Scrath1/Pico-LiDAR/circuit-diagram/circuit-diagram.kicad_pcb

## KiCad design schematics/core_driver.kicad_sch

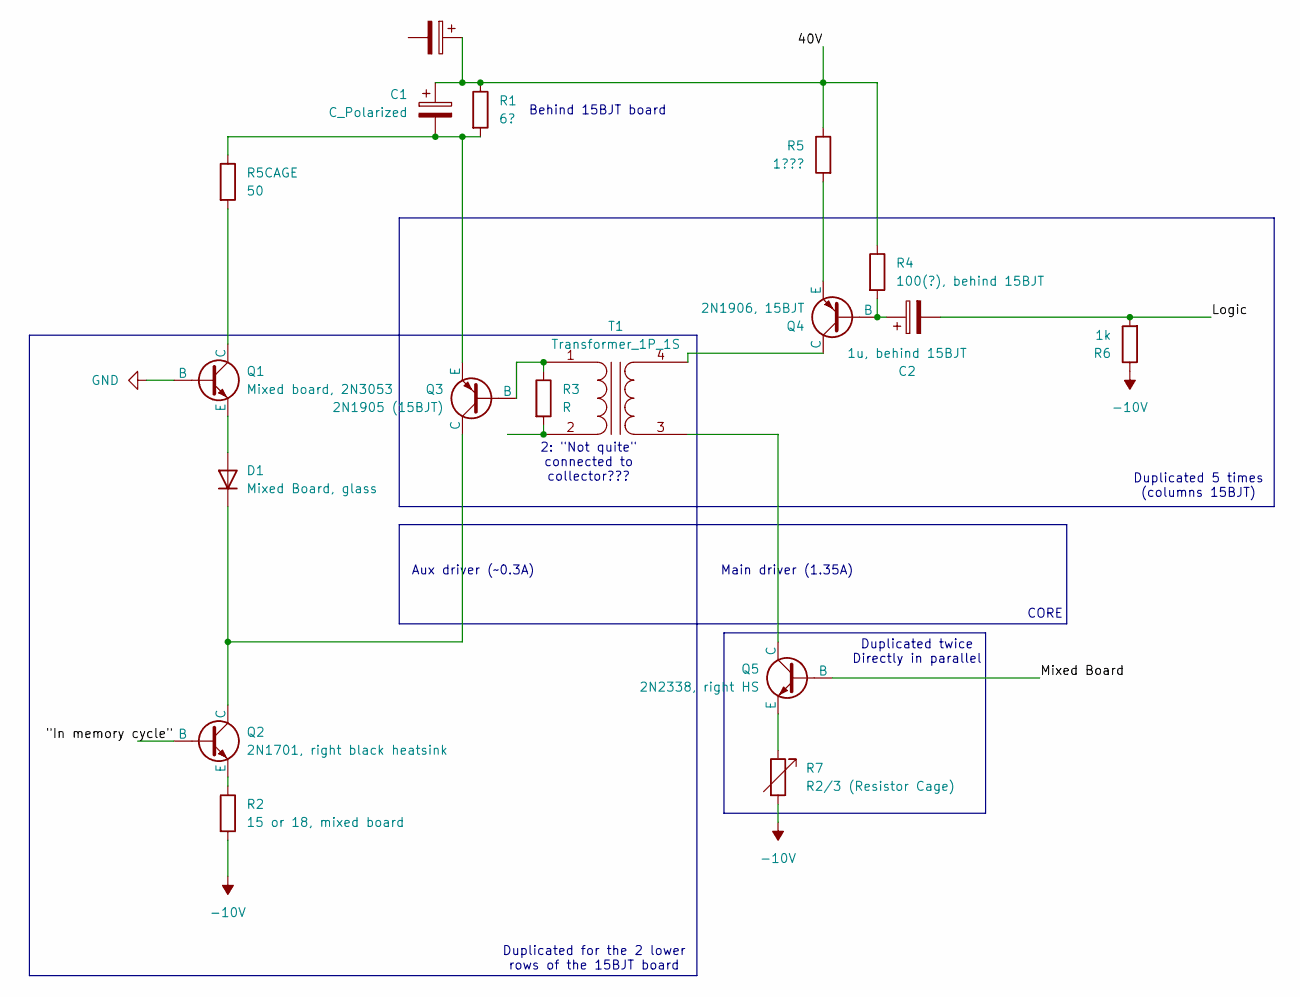
[picture p8: schematic core_driver.kicad_sch]

Parts:
C1: C_Polarized
C2: 1u, behind 15BJT
C8: 4m
D1: Mixed Board, glass
Q1: Mixed board, 2N3053
Q2: 2N1701, right black heatsink
Q3: 2N1905 (15BJT)
Q4: 2N1906, 15BJT
Q5: 2N2338, right HS
R1: 6?
R2: 15 or 18, mixed board
R3: R
R4: 100(?), behind 15BJT
R5: 1???
R5CAGE: 50
R6: 1k
R7: R2/3 (Resistor Cage)
T1: Transformer_1P_1S

Connections:
40V: C1.1, C8.1, R1.1, R4.1, R5.1
"In memory cycle": Q2.2 (B)
-10V: R2.2, R6.1, R7.2
GND: Q1.2 (B)
Logic: C2.2, R6.2
Mixed Board: Q5.2 (B)
unnamed: C1.2, Q3.3 (E), R1.2, R5CAGE.1
unnamed: C2.1, Q4.2 (B), R4.2
unnamed: D1.1 (K), Q2.1 (C), Q3.1 (C)
unnamed: D1.2 (A), Q1.3 (E)
unnamed: Q1.1 (C), R5CAGE.2
unnamed: Q2.3 (E), R2.1
unnamed: Q3.2 (B), R3.1, T1.1 (AA)
unnamed: Q4.1 (C), T1.4 (SB)
unnamed: Q4.3 (E), R5.2
unnamed: Q5.1 (C), T1.3 (SA)
unnamed: Q5.3 (E), R7.1
unnamed: R3.2, T1.2 (AB)

Notes on the sheet:
2: "Not quite" connected to collector???
Duplicated for the 2 lower rows of the 15BJT board
Duplicated 5 times (columns 15BJT)
Aux driver (~0.3A)
Main driver (1.35A)
Duplicated twice Directly in parallel
CORE
Behind 15BJT board
