Scrath1/Pico-LiDAR/circuit-diagram/circuit-diagram.kicad_pcb

## KiCad design schematics/untitled.kicad_sch

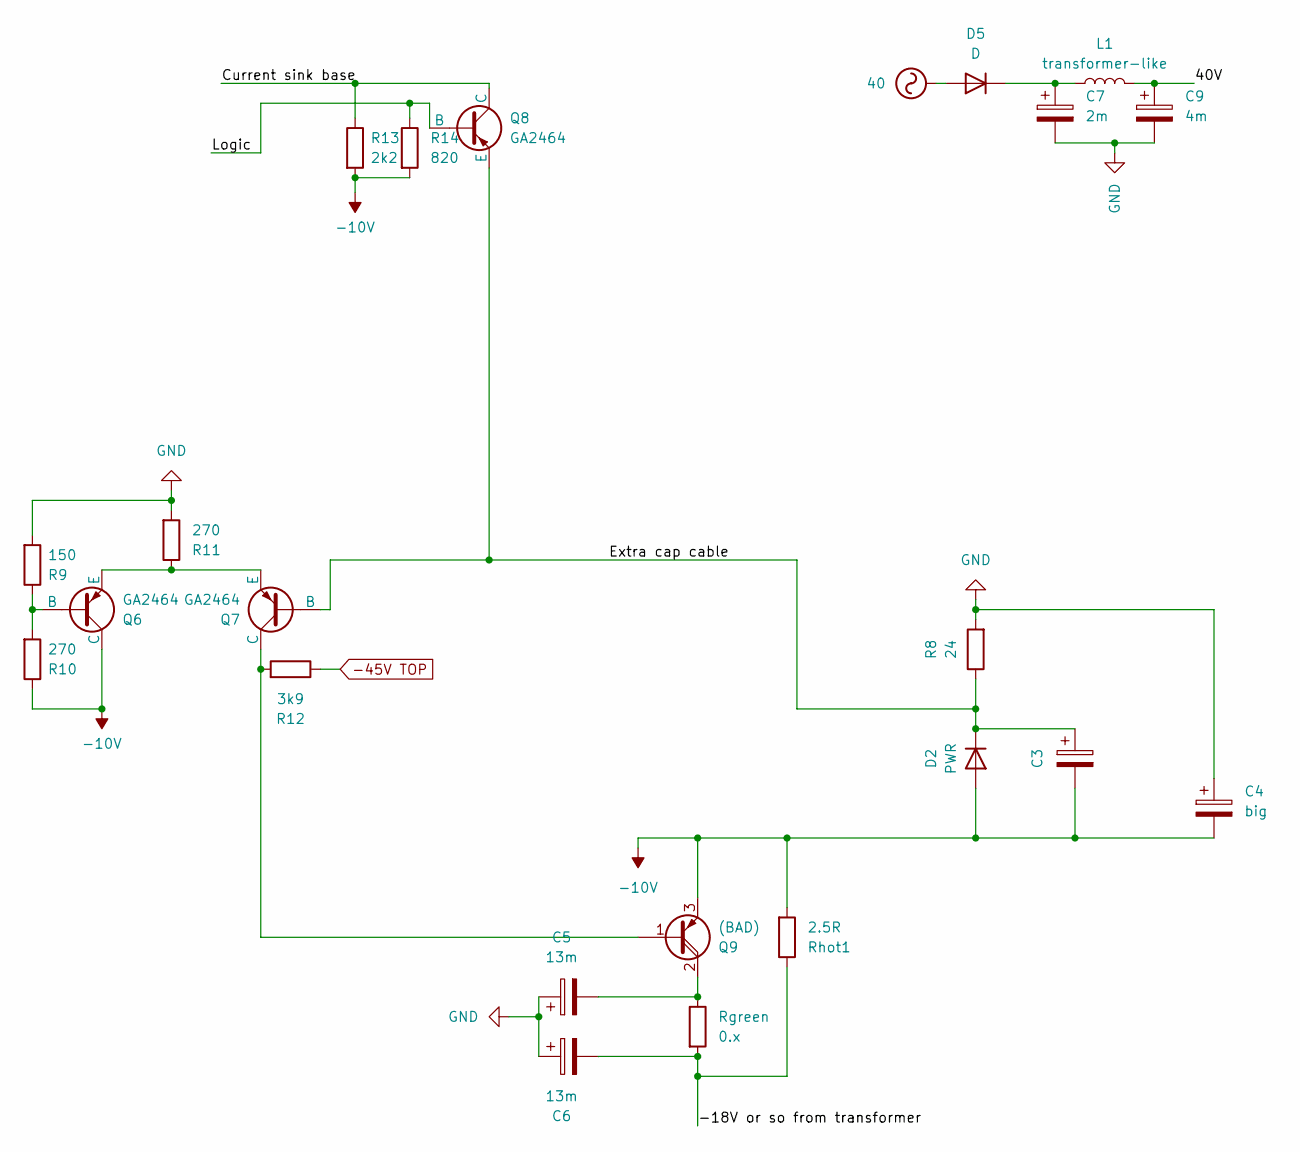
[picture p13: schematic untitled.kicad_sch]

Parts:
C3: offboard
C4: big
C5, C6: 13m
C7: 2m
C9: 4m
D2: PWR
D5: D
L1: transformer-like
Q6, Q7, Q8: GA2464
Q9: (BAD)
R8: 24
R9: 150
R10, R11: 270
R12: 3k9
R13: 2k2
R14: 820
Rgreen: 0.x
Rhot1: 2.5R

Connections:
40: D5.2 (A)
40V: C9.1, L1.2
-10V: C3.2, C4.2, D2.2 (A), Q6.1 (C), Q9.3 (E), R10.1, R13.2, R14.2, Rhot1.2
-18V or so from transformer: C6.2, Rgreen.2, Rhot1.1
-45V TOP: R12.1
Current sink base: Q8.1 (C), R13.1
Extra cap cable: C3.1, D2.1 (K), Q7.2 (B), Q8.3 (E), R8.1
GND: C4.1, C5.1, C6.1, C7.2, C9.2, R8.2, R9.2, R11.2
Logic: Q8.2 (B), R14.1
unnamed: C5.2, Q9.2 (C), Rgreen.1
unnamed: C7.1, D5.1 (K), L1.1
unnamed: Q6.2 (B), R9.1, R10.2
unnamed: Q6.3 (E), Q7.3 (E), R11.1
unnamed: Q7.1 (C), Q9.1 (B), R12.2
