Scrath1/Pico-LiDAR/src/tasks/sensor_task.h

#ifndef SENSOR_TASK_H
#define SENSOR_TASK_H

#include <Arduino.h>
#include <FreeRTOS.h>
#include <task.h>

#define SENSOR_TASK_STACK_SIZE (configMINIMAL_STACK_SIZE)
#define SENSOR_TASK_NAME ("sensorTsk")
#define SENSOR_TASK_PRIORITY (configMAX_PRIORITIES - 1)

#if (SENSOR_TASK_PRIORITY >= configMAX_PRIORITIES)
    #error "Serial interface task priority too high"
#endif

extern TaskHandle_t sensorTaskHandle;
void hc_sr04_isr(BaseType_t& xHigherPriorityTaskWoken, bool risingEdge);
void sensorTask(void* pvParameters);

#endif  // SENSOR_TASK_H
