Scrath1/Pico-LiDAR/src/tasks/motor_control_task.h

#ifndef MOTOR_CONTROL_TASK_H
#define MOTOR_CONTROL_TASK_H

#include <Arduino.h>
#include <FreeRTOS.h>
#include <task.h>

#include "global.h"

#define MOTOR_CONTROL_TASK_STACK_SIZE (configMINIMAL_STACK_SIZE)
#define MOTOR_CONTROL_TASK_NAME ("mtrCtrlTsk")
#define MOTOR_CONTROL_TASK_PRIORITY (configMAX_PRIORITIES - 3)

#if (MOTOR_CONTROL_TASK_PRIORITY >= configMAX_PRIORITIES)
    #error "Motor control task priority too high"
#endif

extern TaskHandle_t motorCtrlTaskHandle;
void motorControlTask(void* pvParameters);

#endif  // MOTOR_CONTROL_TASK_H
