Scrath1/Pico-LiDAR/src/data_types/status.h

#ifndef STATUS_H
#define STATUS_H

#include <cstdint>

#include "dome_angle.h"
#include "rpm_data.h"

typedef struct {
    rpm_data_t measuredRPM;
    bool stableTargetRPM;
    uint32_t stableTargetRPMCount;
    uint32_t sensorTaskInterval_ms;
    dome_angle_t domeAngle;
    uint16_t pwmOutputLevel;
    uint32_t serialCmdErrors;
} status_t;

#endif  // STATUS_H
