Scrath1/Pico-LiDAR/src/data_types/rpm_data.h

#ifndef RPM_DATA_H
#define RPM_DATA_H
#include <FreeRTOS.h>
#include <task.h>

#include <cstdint>

typedef struct {
    uint32_t rpm;
    uint32_t timestampLastChanged_ms;

    void set(uint32_t rpm) {
        this->rpm = rpm;
        timestampLastChanged_ms = pdTICKS_TO_MS(xTaskGetTickCount());
    }

    void setFromISR(uint32_t rpm) {
        this->rpm = rpm;
        timestampLastChanged_ms = pdTICKS_TO_MS(xTaskGetTickCountFromISR());
    }

    uint32_t getAge_ms() { return pdTICKS_TO_MS(xTaskGetTickCount()) - timestampLastChanged_ms; }
} rpm_data_t;

#endif  // RPM_DATA_H
