Scrath1/Pico-LiDAR/src/serial_print.cpp

#include "serial_print.h"

#include <Arduino.h>

#include <cstdio>

#include "prj_config.h"
#include "tasks/serial_tx_task.h"

volatile bool useTxTask;

void serialPrint(const char* msg) {
    if(useTxTask) {
        uint32_t len = strlen(msg) + 1;  // +1 to include the null-terminator
        serialPrint(msg, len);
    } else {
        SERIAL_PORT.print(msg);
    }
}

void serialPrint(const char* msg, uint32_t msgLen) {
    if(useTxTask) {
        putString(msg, msgLen);
    } else {
        SERIAL_PORT.print(msg);
    }
}

void serialPrintf(const char* fmt, ...) {
    va_list args;
    va_start(args, fmt);

    char buf[DBG_MESSAGE_MAX_LEN];
    uint32_t len = vsnprintf(buf, DBG_MESSAGE_MAX_LEN, fmt, args);
    va_end(args);
    serialPrint(buf, len + 1);
}
