Scrath1/Pico-LiDAR/src/tasks/signal_age_check_task.h

#ifndef SIGNAL_AGE_CHECK_TASK_H
#define SIGNAL_AGE_CHECK_TASK_H

#include <Arduino.h>
#include <FreeRTOS.h>
#include <task.h>

#define SIGNAL_AGE_CHECK_TASK_STACK_SIZE (configMINIMAL_STACK_SIZE)
#define SIGNAL_AGE_CHECK_TASK_NAME ("sigAgeChkTsk")
#define SIGNAL_AGE_CHECK_TASK_PRIORITY (configMAX_PRIORITIES - 3)

#if (SIGNAL_AGE_CHECK_TASK_PRIORITY >= configMAX_PRIORITIES)
    #error "Signal age check task priority too high"
#endif

extern TaskHandle_t signalAgeCheckTaskHandle;
void signalAgeCheckTask(void* pvParameters);

#endif  // SIGNAL_AGE_CHECK_TASK_H
