Scrath1/Pico-LiDAR/interface-script/mplcanvas.py

import matplotlib
matplotlib.use('QtAgg')
from matplotlib.backends.backend_qt5agg import FigureCanvasQTAgg
from matplotlib.figure import Figure

class MplCanvas(FigureCanvasQTAgg):
    def __init__(self, parent=None, width=5, height=4, dpi=100):
        self.fig = Figure(figsize=(width, height), dpi=dpi)
        super().__init__(self.fig)
